219-design/219-pcb-ruler/firmware/ruler_lib/examples/digital_level/219 PCB Ruler -- level.png

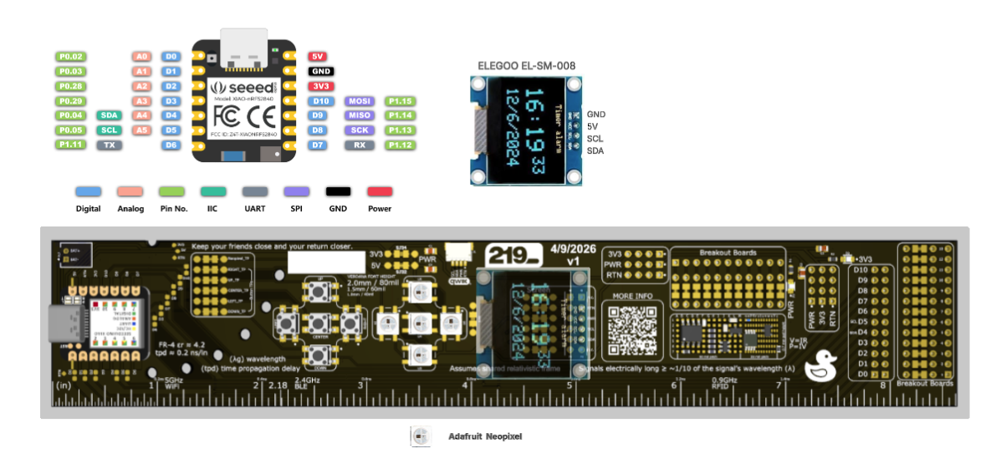
firmware/ruler_lib/examples/digital_level/219 PCB Ruler -- level.png
