219-design/219-pcb-ruler/firmware/ruler_lib/examples/simon/219 PCB Ruler -- simon.png

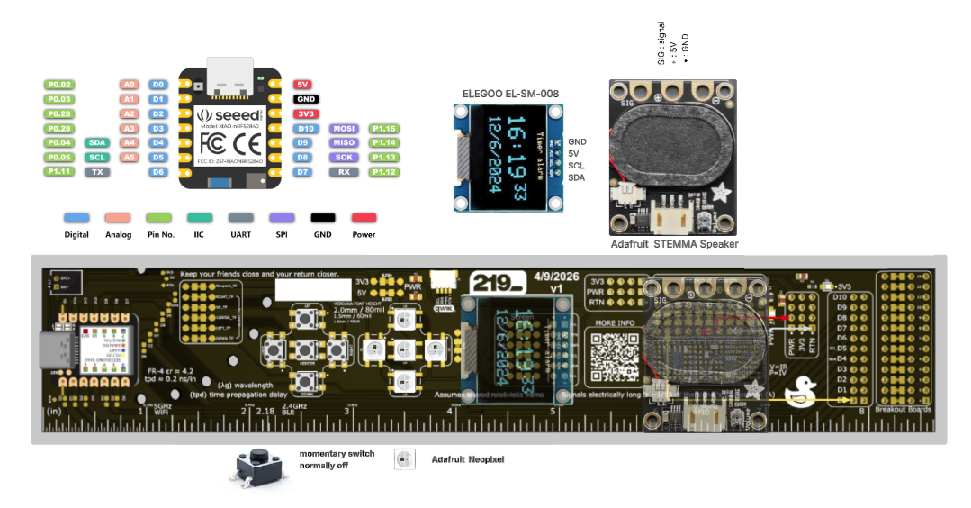
firmware/ruler_lib/examples/simon/219 PCB Ruler -- simon.png
