219-design/219-pcb-ruler/photos/bare_boards.jpg

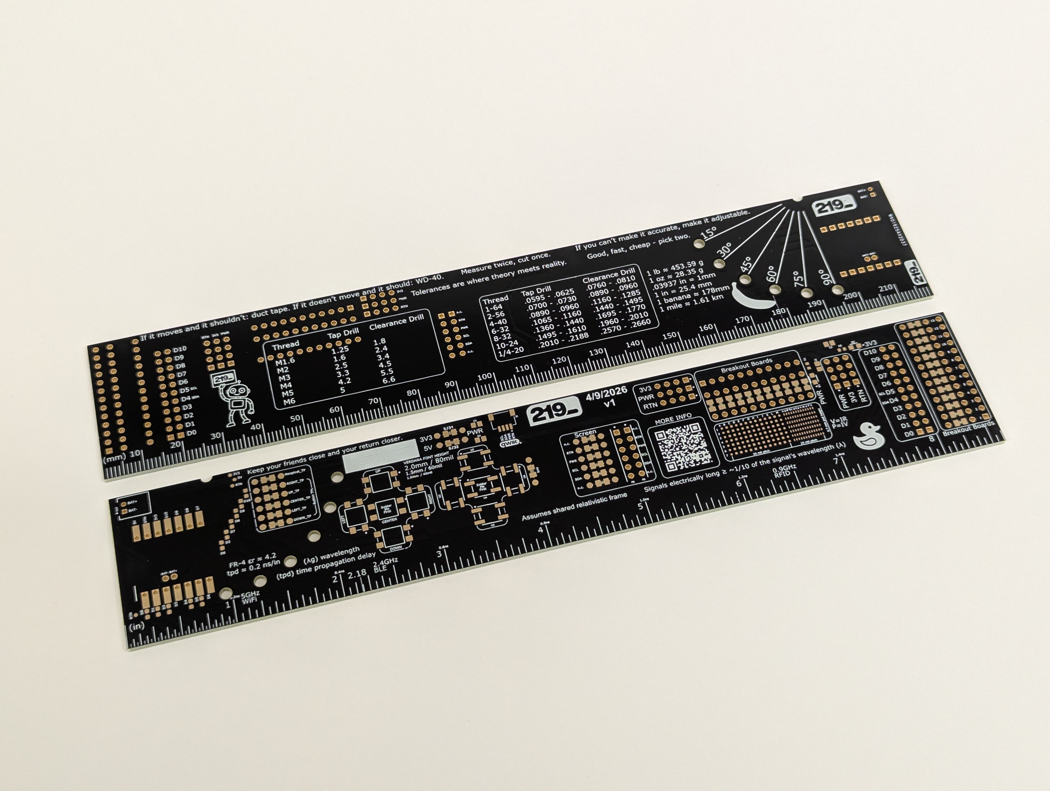
photos/bare_boards.jpg
